matgla/mspc/mainboard/mainboard/docs/hs8836a/H2b1801c37de748d28c753530b9616148l.jpg_.webp

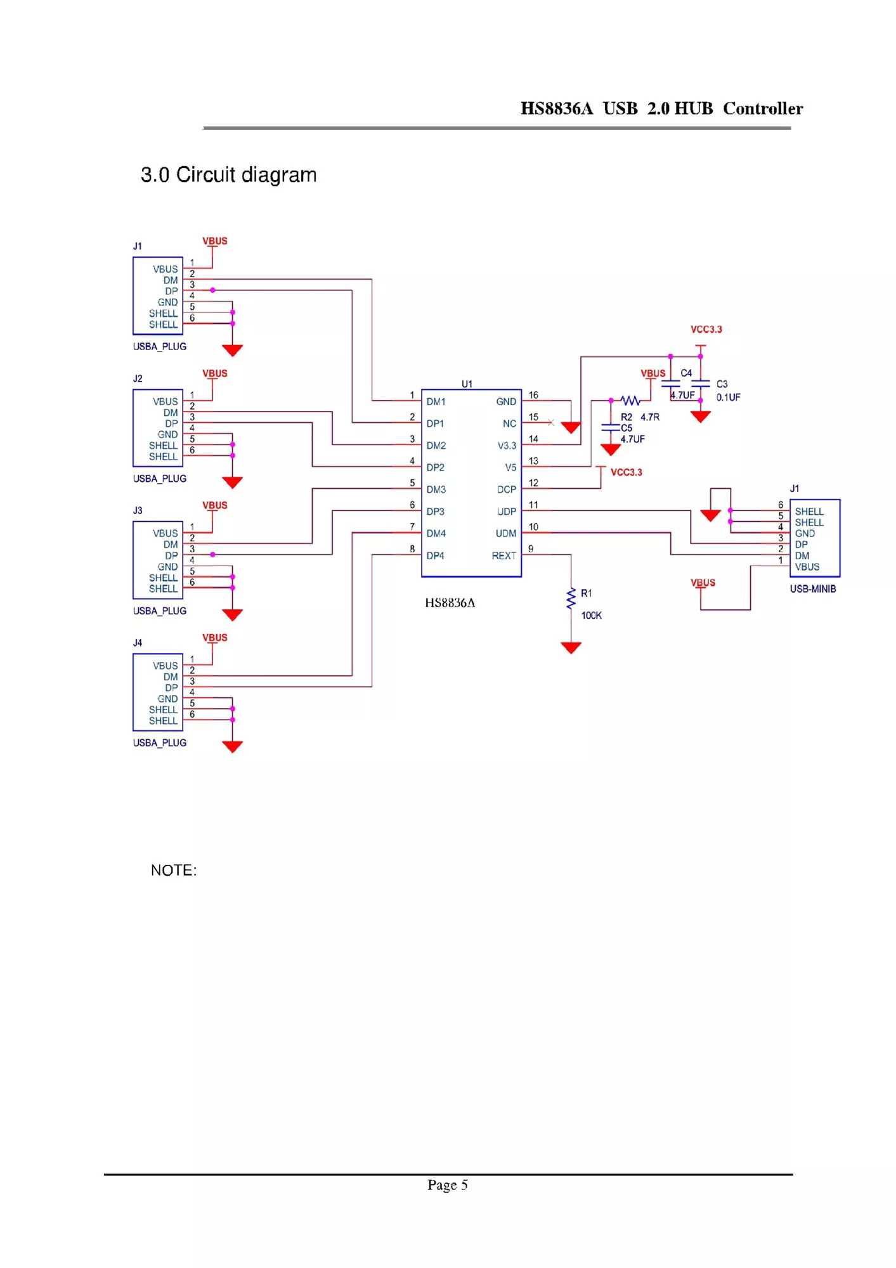
mainboard/mainboard/docs/hs8836a/H2b1801c37de748d28c753530b9616148l.jpg_.webp
