matgla/mspc/mainboard/mainboard/docs/hs8836a/Hc5890efedd604732949321075c03d67dT.jpg_.webp

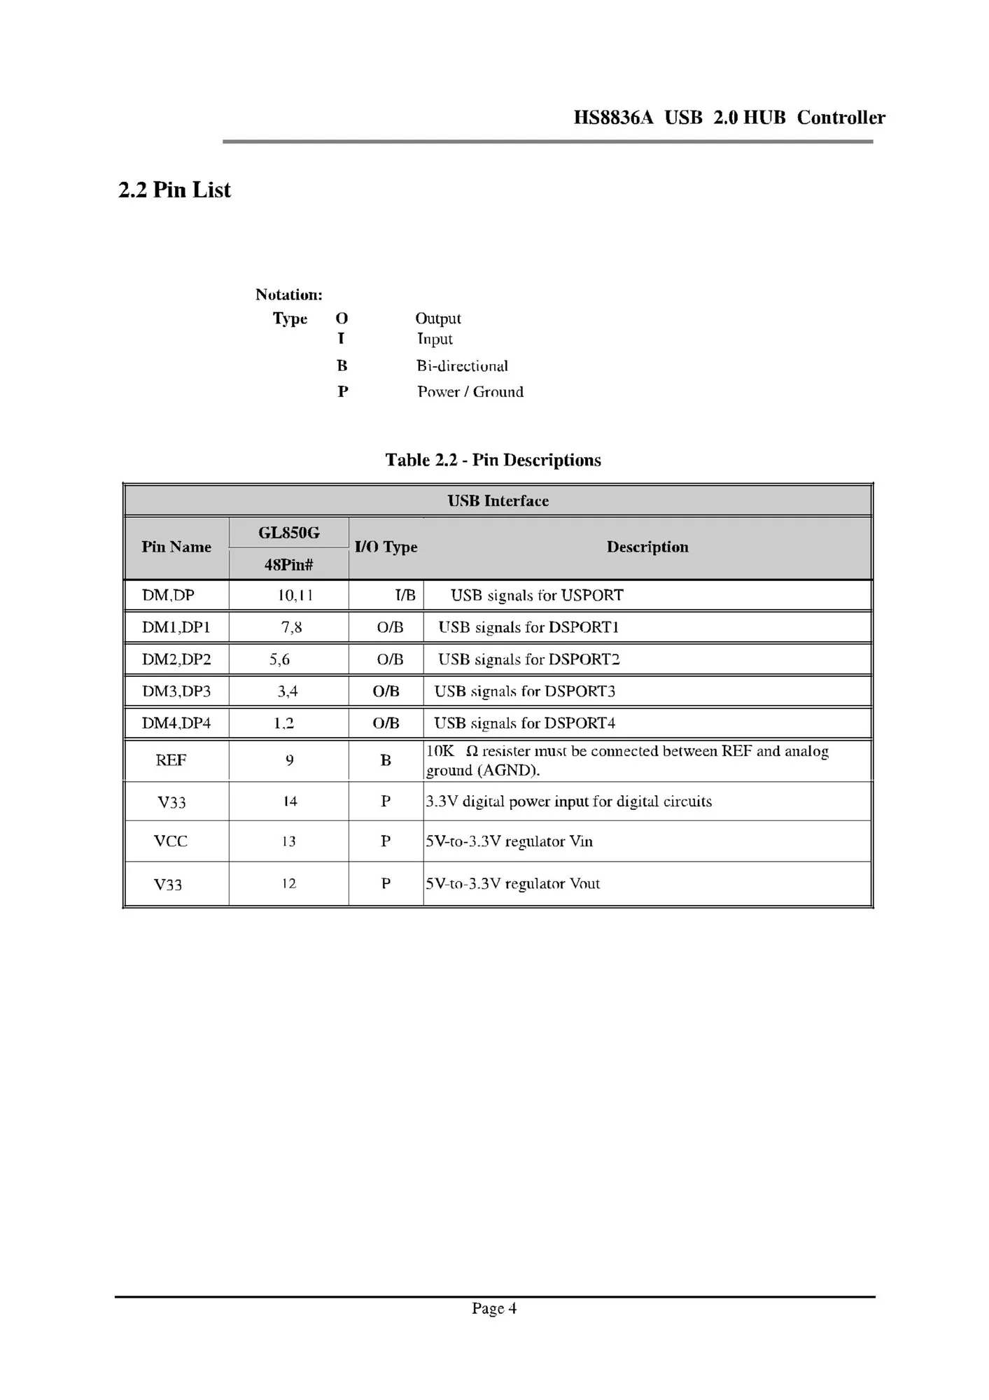
mainboard/mainboard/docs/hs8836a/Hc5890efedd604732949321075c03d67dT.jpg_.webp
