matgla/mspc/mainboard/mainboard/docs/hs8836a/Hdc688dac686e4d4f9e8fb63737b41098C.jpg_.webp

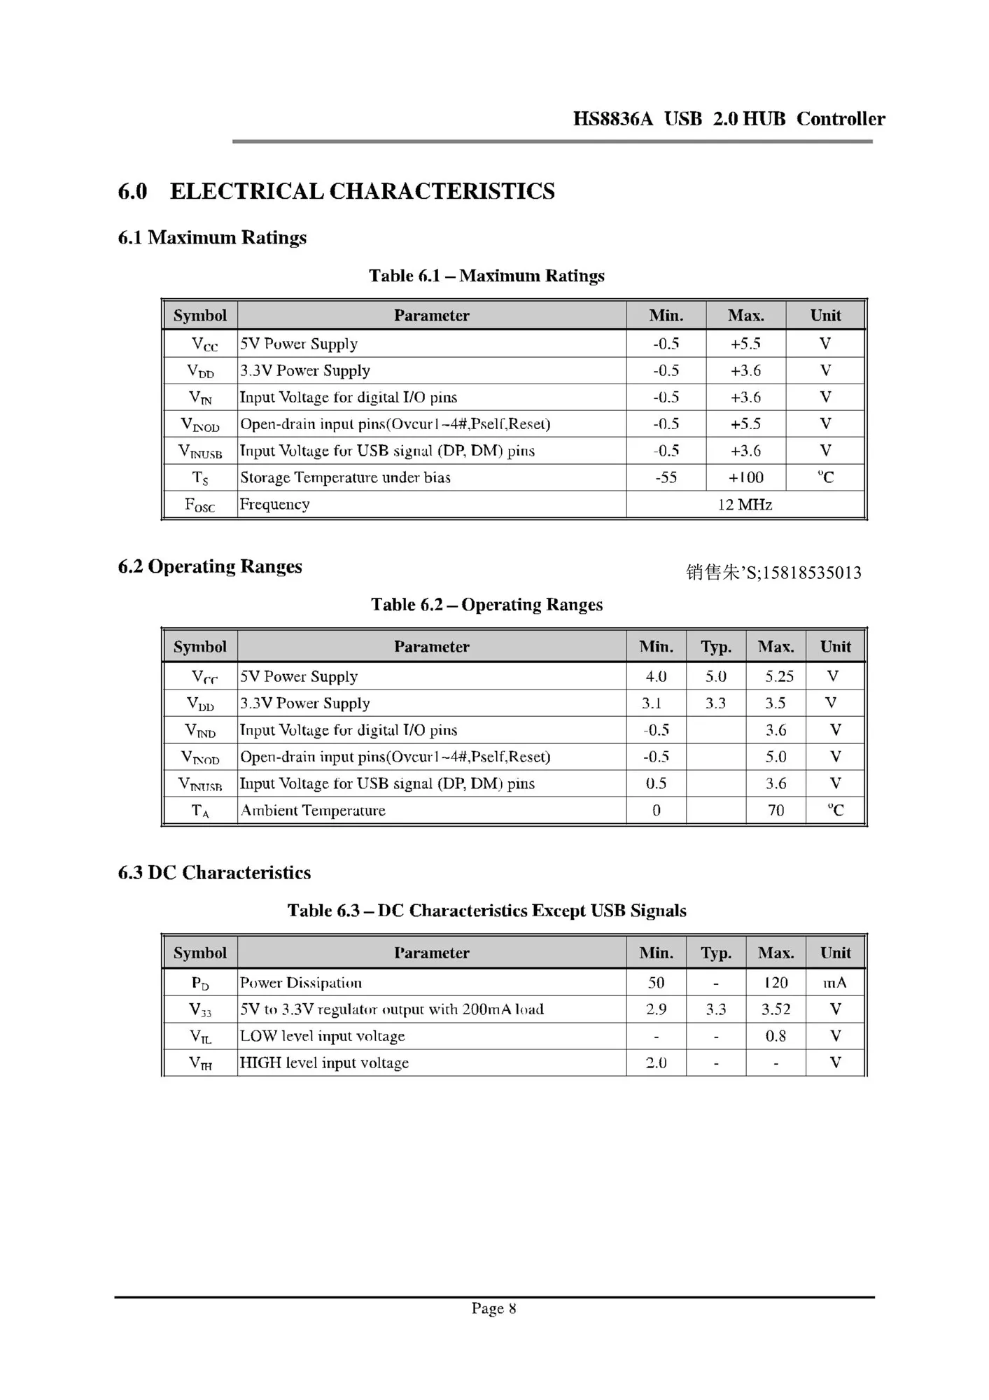
mainboard/mainboard/docs/hs8836a/Hdc688dac686e4d4f9e8fb63737b41098C.jpg_.webp
